kanflo/commadorable-64/Arduino_C64/data/c64.bmp

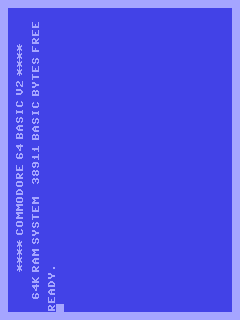
Arduino_C64/data/c64.bmp
